whowechina/arcade_pico/PCB/button_dip_led/3dmodels/User Library-WS2812-4020.step

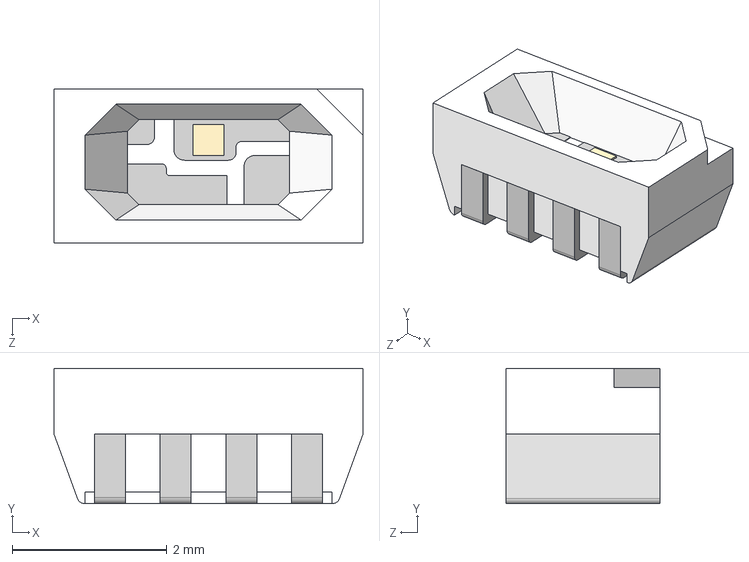
[picture p33: CAD file, 2025-12-19]
PCB/button_dip_led/3dmodels/User Library-WS2812-4020.step
4.00 x 1.75 x 2.00 mm
