whowechina/arcade_pico/firmware/src/commands.c

#include <stdio.h>
#include <stdlib.h>
#include <string.h>
#include <fcntl.h>
#include <ctype.h>

#include "pico/stdio.h"
#include "pico/stdlib.h"

#include "config.h"
#include "save.h"
#include "cli.h"

#include "hebtn.h"

#include "usb_descriptors.h"

#define SENSE_LIMIT_MAX 9
#define SENSE_LIMIT_MIN -9

static void disp_light()
{
    printf("[Light]\n");
    printf("  Level: %d.\n", arcade_cfg->light.level);
}

static void disp_hall()
{
    printf("[Hall Effect Button]\n");
    for (int i = 0; i < hebtn_keynum(); i++) {
        if (!hebtn_present(i)) {
            printf("  Key %2d: Not Present.\n", i + 1);
            continue;
        }
        printf("  Key %2d: %4d->%4d, On: %2d, Off: %2d.\n",
               i + 1, arcade_cfg->calibrated.up[i], arcade_cfg->calibrated.down[i],
                arcade_cfg->trigger.on[i] + 1, arcade_cfg->trigger.off[i] + 1);
    }
}

static void disp_route()
{
    printf("[Route]\n");
    printf("  Hall In |  1  2  3  4  5  6  7  8\n");
    printf("  --> Out |");
    for (int i = 0; i < count_of(arcade_cfg->route.output); i++) {
        printf("%3d", (arcade_cfg->route.output[i] % 8) + 1);
    }
    printf("\n  --------\n");

    printf("  Lamp In |  1  2  3  4  5  6  7  8\n");
    printf("  --> RGB |");
    for (int i = 0; i < count_of(arcade_cfg->route.rgb); i++) {
        printf("%3d", (arcade_cfg->route.rgb[i] % 8) + 1);
    }
    printf("\n");
}

void handle_display(int argc, char *argv[])
{
    const char *usage = "Usage: display [light|he|route]\n";
    if (argc > 1) {
        printf(usage);
        return;
    }

    if (argc == 0) {
        disp_light();
        disp_hall();
        disp_route();
        return;
    }

    const char *choices[] = {"light", "he", "route"};
    switch (cli_match_prefix(choices, count_of(choices), argv[0])) {
        case 0:
            disp_light();
            break;
        case 1:
            disp_hall();
            break;
        case 2:
            disp_route();
            break;
        default:
            printf(usage);
            break;
    }
}

static void handle_level(int argc, char *argv[])
{
    const char *usage = "Usage: level <0..255>\n";
    if (argc != 1) {
        printf(usage);
        return;
    }

    int level = cli_extract_non_neg_int(argv[0], 0);
    if ((level < 0) || (level > 255)) {
        printf(usage);
        return;
    }

    arcade_cfg->light.level = level;
    config_changed();
    disp_light();
}

static void handle_calibrate(int argc, char *argv[])
{
    hebtn_calibrate();
}

static void handle_trigger(int argc, char *argv[])
{
    const char *usage = "Usage: trigger <all|KEY> <ON> <OFF>\n"
                        "  KEY: 1..%d\n"
                        "   ON: 1..36, distance for actuation.\n"
                        "  OFF: 1..36, distance for reset.\n";
    if (argc != 3) {
        printf(usage, hebtn_keynum());
        return;
    }

    bool all_key = (strncasecmp(argv[0], "all", strlen(argv[0])) == 0);
    int key = cli_extract_non_neg_int(argv[0], 0) - 1;
    int on = cli_extract_non_neg_int(argv[1], 0) - 1;
    int off = cli_extract_non_neg_int(argv[2], 0) - 1;
    
    if ((!all_key && (key < 0)) || (key >= hebtn_keynum()) ||
        (on < 0) || (on > 35) || (off < 0) || (off > 35)) {
        printf(usage, hebtn_keynum());
        return;
    }

    for (int i = 0; i < hebtn_keynum(); i++) {
        if (all_key || (i == key)) {
            arcade_cfg->trigger.on[i] = on;
            arcade_cfg->trigger.off[i] = off;
        }
    }
    config_changed();

    disp_hall();
}

static void handle_route(int argc, char *argv[])
{
    const char *usage = "Usage: route <output|rgb> <KEY> <VALUE>\n"
                        "  KEY: 1..8\n"
                        " VALUE: 1..8\n";
    if (argc != 3) {
        printf(usage);
        return;
    }

    const char *choices[] = {"output", "rgb"};
    int field = cli_match_prefix(choices, count_of(choices), argv[0]);
    if (field < 0) {
        printf(usage);
        return;
    }

    int key = cli_extract_non_neg_int(argv[1], 0) - 1;
    int value = cli_extract_non_neg_int(argv[2], 0) - 1;
    if ((key < 0) || (key >= 8) || (value < 0) || (value >= 8)) {
        printf(usage);
        return;
    }

    if (field == 0) {
        arcade_cfg->route.output[key] = value;
    } else {
        arcade_cfg->route.rgb[key] = value;
    }

    config_changed();
    disp_route();
}

static void handle_debug(int argc, char *argv[])
{
    const char *usage = "Usage: debug <hall|input>\n";
    if (argc != 1) {
        printf(usage);
        return;
    }
    const char *choices[] = {"hall", "input"};
    switch (cli_match_prefix(choices, count_of(choices), argv[0])) {
        case 0:
            arcade_runtime.debug.hall ^= true;
            hebtn_debug(arcade_runtime.debug.hall);
            break;
        case 1:
            arcade_runtime.debug.input ^= true;
            break;
        default:
            printf(usage);
            break;
    }
}

static void handle_save()
{
    save_request(true);
}

static void handle_factory_reset()
{
    config_factory_reset();
    printf("Factory reset done.\n");
}

void commands_init()
{
    cli_register("display", handle_display, "Display all config.");
    cli_register("level", handle_level, "Set LED brightness level.");
    cli_register("calibrate", handle_calibrate, "Calibrate the key sensors.");
    cli_register("trigger", handle_trigger, "Set Hall effect switch triggering.");
    cli_register("route", handle_route, "Set output and rgb routing.");
    cli_register("debug", handle_debug, "Toggle debug features.");
    cli_register("save", handle_save, "Save config to flash.");
    cli_register("factory", handle_factory_reset, "Reset everything to default.");
}
